loidolt/concrete-countertops/3d-model/Kitchen/Sink.png

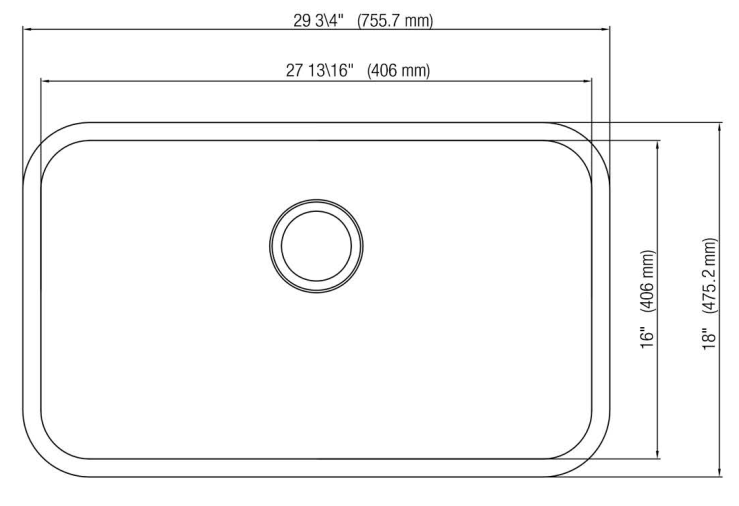
3d-model/Kitchen/Sink.png
